Lenart12/kresnik/esp32-HRC/include/PCF8574_WDDR.h

#ifndef PCF8574_WDDR_H
#define PCF8574_WDDR_H

#include <PCF8574.h>

class PCF8574_WDDR : public virtual PCF8574{
public:
	void writeDDR(uint8_t value);
protected:
	void updateGPIO() override;
	void readGPIO() override;
};

#endif
