Lenart12/kresnik/esp32-HRC/include/logging.h

#ifndef LOGGING_H
#define LOGGING_H

#include <lvgl.h>
#include <Arduino.h>
#include <globals.h>

#if 0
void logging_cb(lv_log_level_t level, const char * file, uint32_t line, const char * dsc){
    if(level == LV_LOG_LEVEL_ERROR){
        status_expander.digitalWrite(Status_led::error, ON);
        lv_task_enable(false);
        digitalWrite(TFT_LED, ON);
        relay0_expander.write(0xFF);
        relay1_expander.write(0xFF);
        thermo_expander.write(0xFF);
        lv_obj_t *scr =  lv_cont_create(NULL, NULL);
        lv_disp_load_scr(scr);
        lv_obj_t * label = lv_label_create(scr, NULL);
        String err = LV_SYMBOL_WARNING +  (String)"ERROR: File: " + file + '#' + line + "\n " + dsc;
        Serial.print((String)"\033[91mERROR:\033[0m File: " + file + '#' + line + "\n " + dsc);
        lv_label_set_text(label, err.c_str());
        lv_obj_align(label, NULL, LV_ALIGN_CENTER, 0, 0);
    }
    else if(level == LV_LOG_LEVEL_WARN)  Serial.print("\033[93mWARNING:\033[0m ");
    else if(level == LV_LOG_LEVEL_INFO)  Serial.print("\033[94mINFO:\033[0m ");
    else if(level == LV_LOG_LEVEL_TRACE) Serial.print("TRACE: ");

    Serial.print("File: ");
    Serial.print(file);

    char line_str[8];
    sprintf(line_str,"%d", line);
    Serial.print("#");
    Serial.print(line_str);

    Serial.print(": ");
    Serial.print(dsc);
    Serial.print("\n");
}
#endif

void logging_cb(lv_log_level_t level, const char * file, uint32_t line, const char * fn_name, const char * dsc)
{
  /*Send the logs via serial port*/
  if(level == LV_LOG_LEVEL_ERROR) Serial.print("ERROR: ");
  if(level == LV_LOG_LEVEL_WARN)  Serial.print("WARNING: ");
  if(level == LV_LOG_LEVEL_INFO)  Serial.print("INFO: ");
  if(level == LV_LOG_LEVEL_TRACE) Serial.print("TRACE: ");

  Serial.print("File: ");
  Serial.print(file);

  char line_str[8];
  sprintf(line_str,"%d", line);
  Serial.print("#");
  Serial.print(line_str);

  Serial.print(": ");
  Serial.print(fn_name);
  Serial.print(": ");
  Serial.print(dsc);
  Serial.print("\n");
}

#endif
