Lenart12/kresnik/esp32-HRC/src/globals.cpp

#include <globals.h>

SemaphoreHandle_t i2c_mutex = xSemaphoreCreateMutex();
SemaphoreHandle_t timing_mutex = xSemaphoreCreateMutex();
SemaphoreHandle_t tempature_mutex= xSemaphoreCreateMutex();

bool minute_update;

lv_task_t *update_task_h;
lv_task_t *request_temp_task_h;
lv_task_t *screensaver_task_h;

PCF8574_WDDR status_expander;
PCF8574_WDDR thermo_expander;
PCF8574_WDDR relay0_expander;
PCF8574_WDDR relay1_expander;

Config config;

OneWire ds2482_0(DS2482_0);
OneWire ds2482_1(DS2482_1);
DallasTemperature tempature_1(&ds2482_0);
DallasTemperature tempature_2(&ds2482_1);

Ticker tick;
Ticker conversion_ticker;
TFT_eSPI tft = TFT_eSPI();

lv_disp_buf_t disp_buf;
lv_color_t buf[LV_HOR_RES_MAX * 10];
lv_point_t button_targets[4];

Ticker motor_tickers[4];
xSemaphoreHandle motor_mutexes[4] = {
    xSemaphoreCreateMutex(),
    xSemaphoreCreateMutex(),
    xSemaphoreCreateMutex(),
    xSemaphoreCreateMutex()
};

float boiler_temp[24] = {0};
float hot_water_container_temp[24] = {0};
float enviroment_temp[24] = {0};
float underfloor_temp[4][24] = {0};
float solar_collector_temp[24] = {0};
float solar_tank_temp[24] = {0};
float heat_exchanger_temp[24] = {0};
